UBO-Open-factory/Borne-satisfaction/Programmation/Main program/illustrations/Arduino_CardChoice.png

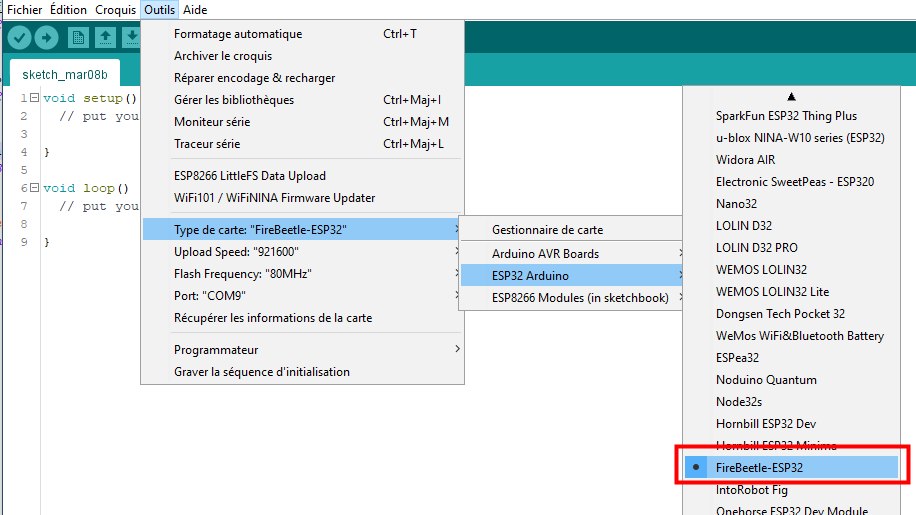
Programmation/Main program/illustrations/Arduino_CardChoice.png
