UBO-Open-factory/Borne-satisfaction/Programmation/Main program/illustrations/Arduino_ESP32.png

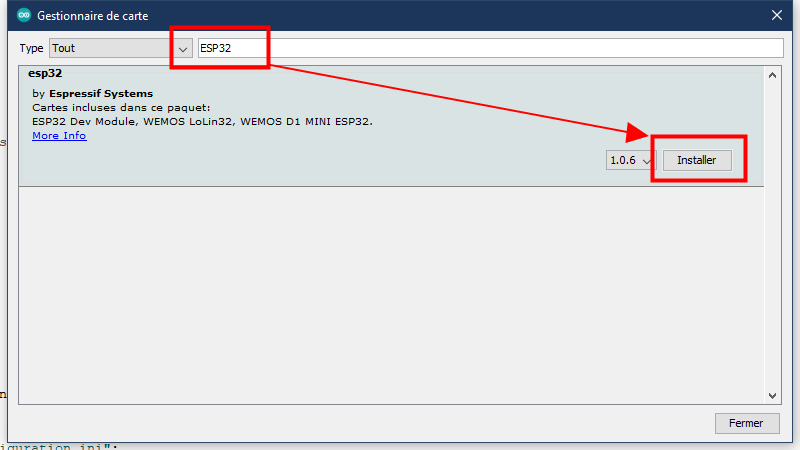
Programmation/Main program/illustrations/Arduino_ESP32.png
