UBO-Open-factory/Borne-satisfaction/Programmation/Main program/illustrations/Arduino_preferences.png

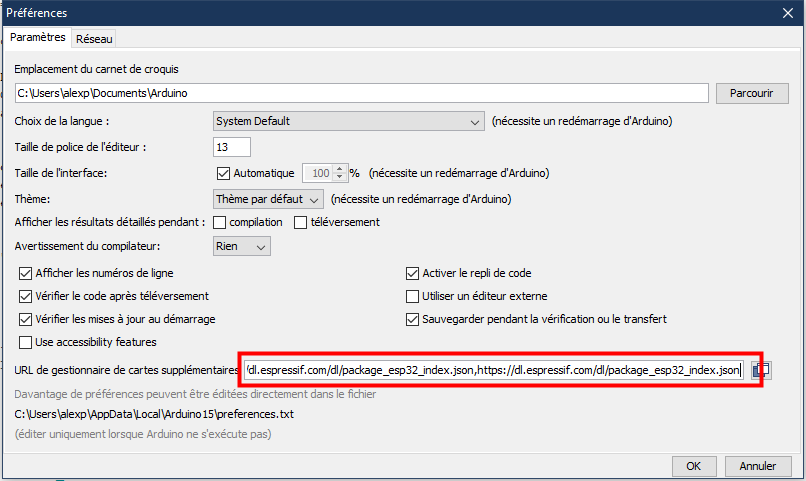
Programmation/Main program/illustrations/Arduino_preferences.png
