UBO-Open-factory/Borne-satisfaction/Programmation/Main program/illustrations/Diagrams.png

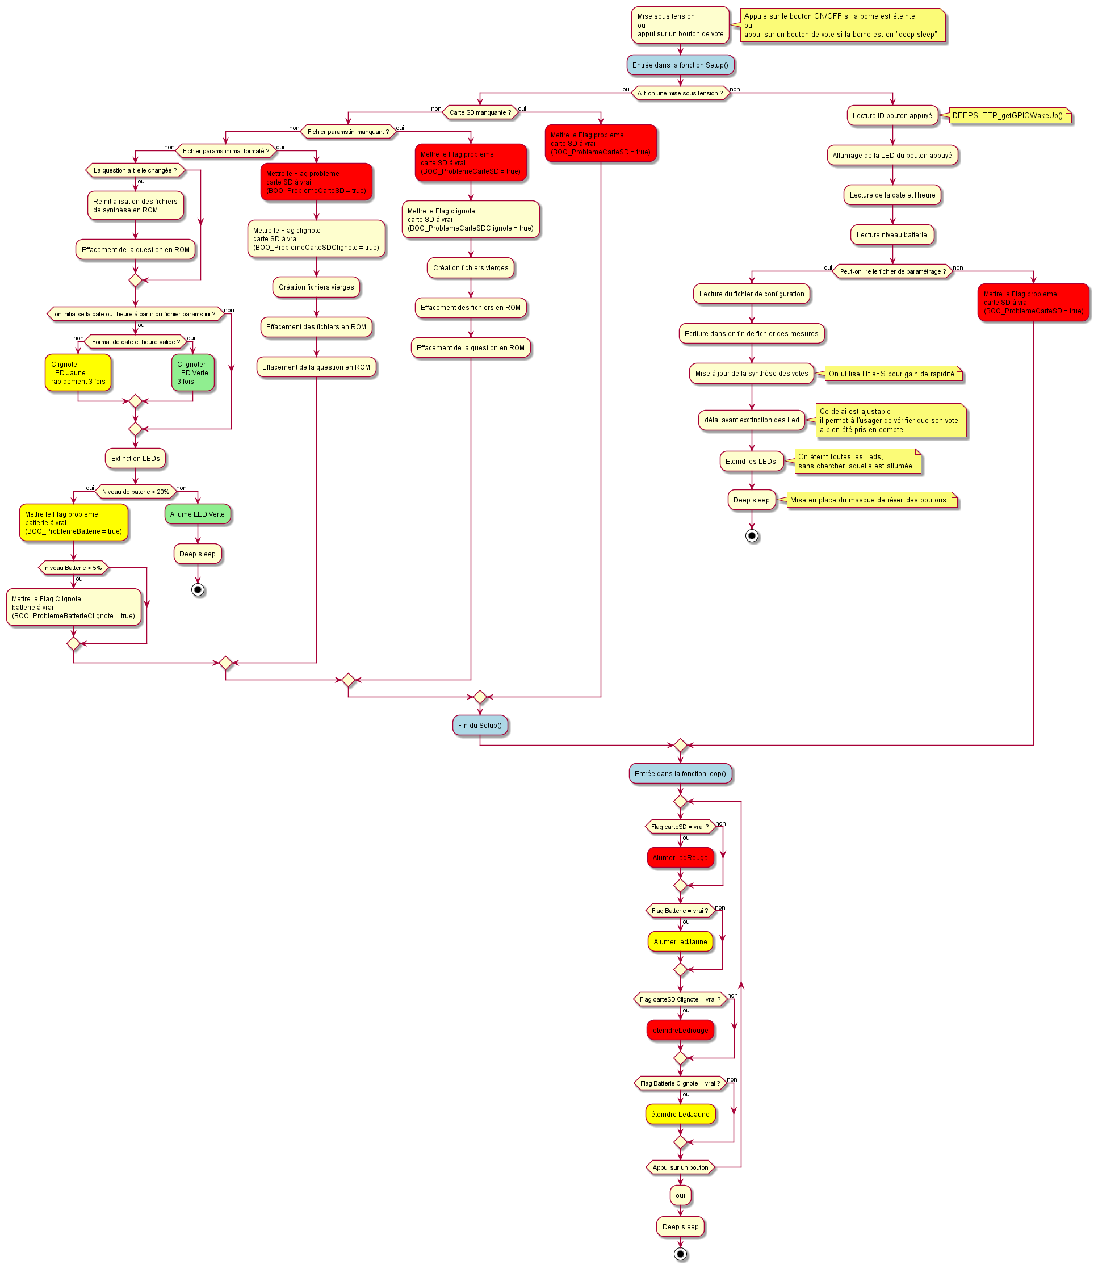
Programmation/Main program/illustrations/Diagrams.png
