UBO-Open-factory/Borne-satisfaction/Programmation/Main program/BorneSatisfaction/Batterie.h

/**
 * @file Batterie.h
 * @author Alexandre PERETJATKO (peretjatko@univ-brest.fr)
 * @brief contains all function for battery purpose.
 * @date 2022-05-10
 * @version 1.0.2
 * 
 */
// _______________________________________________________________________________________

/**
 -----------------------------------------------------------------------------------------
 @brief Renvoie le niveau de la batterie en pourcentage (sans le signe).
 @version issue #10 : Protection contre des valeurs négatifs du pourcentage (si < 0, on renvoie 0 ) et si on a un pourcent > 100
 @return int contenant le pourcentage du niveau de charge de la batterie.
*/
int BATTERIE_getBatterieLevel() {
  float mesureTensionMAX = 2425;
  float mesureTensionMIN = 1725;

  // Renvoie la tension
  int tension = (int) analogRead(A0);
  DEBUG("Mesure analogique renvoyee par la batterie:  " + String(tension));


  // Calcul du pourcentage
  // On ne garde que la partie entière de la valeur
  int pourcent = (int) 100 / (mesureTensionMAX - mesureTensionMIN) * (tension - mesureTensionMIN);
  if( pourcent < 0 ) {
    return 0;
  }
  if( pourcent > 100 ) {
    return 100;
  }

  return pourcent;
}
